mzero/pulsar-buddy/board/Pulsar Buddy SM grn.png

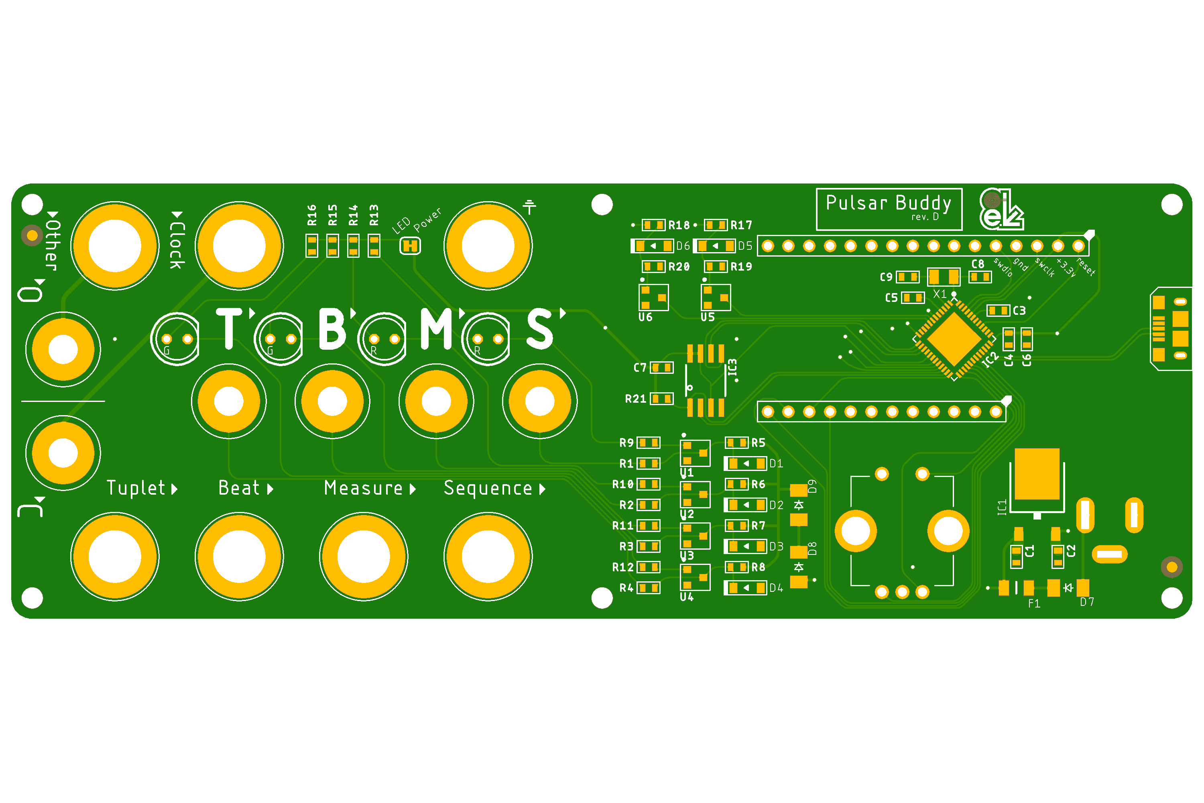
board/Pulsar Buddy SM grn.png
