mzero/pulsar-buddy/board/Pulsar Buddy SM.png

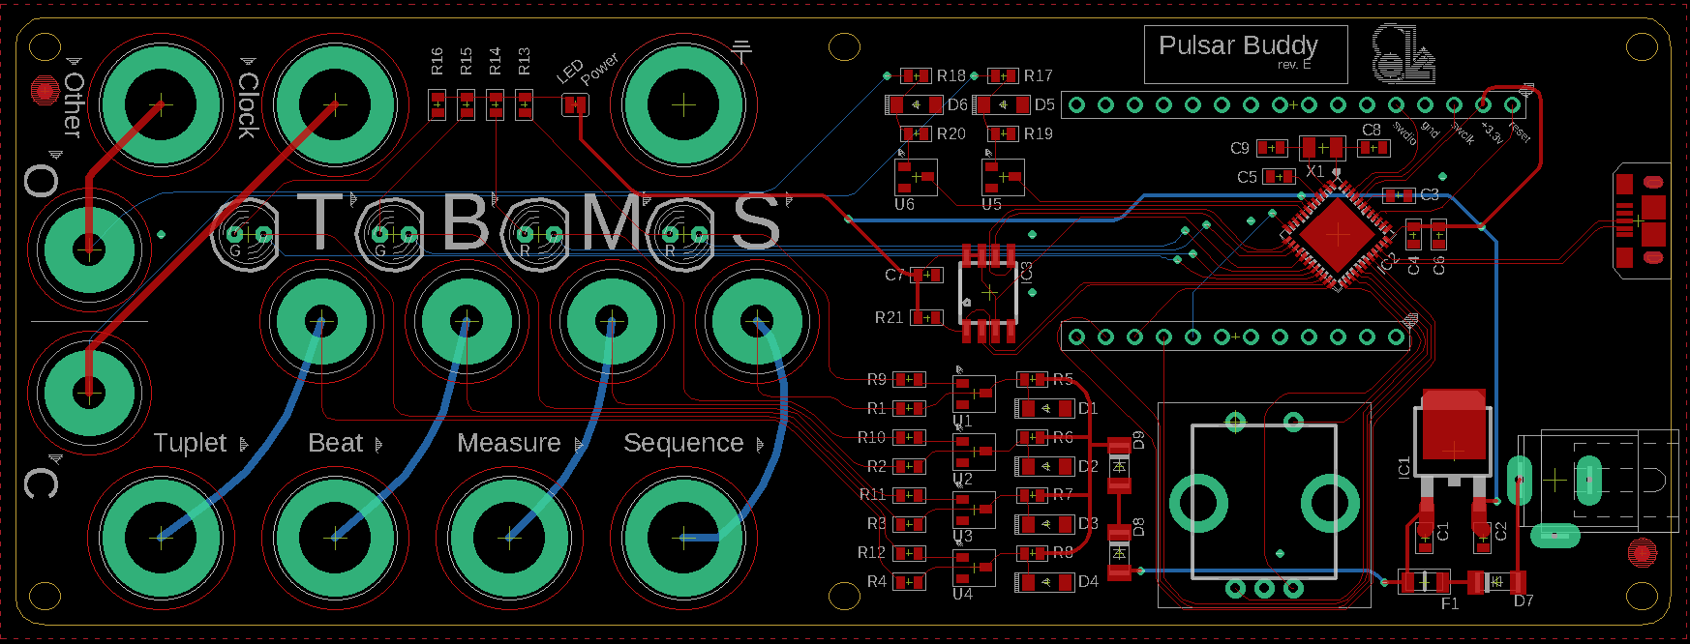
board/Pulsar Buddy SM.png
