mzero/pulsar-buddy/wiki-images/box1.jpg

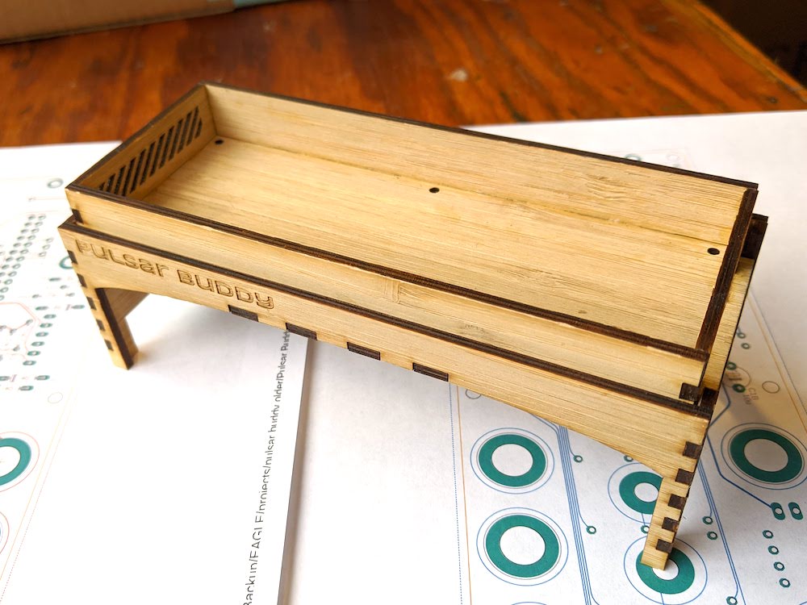
wiki-images/box1.jpg
