mzero/pulsar-buddy/wiki-images/box2.jpg

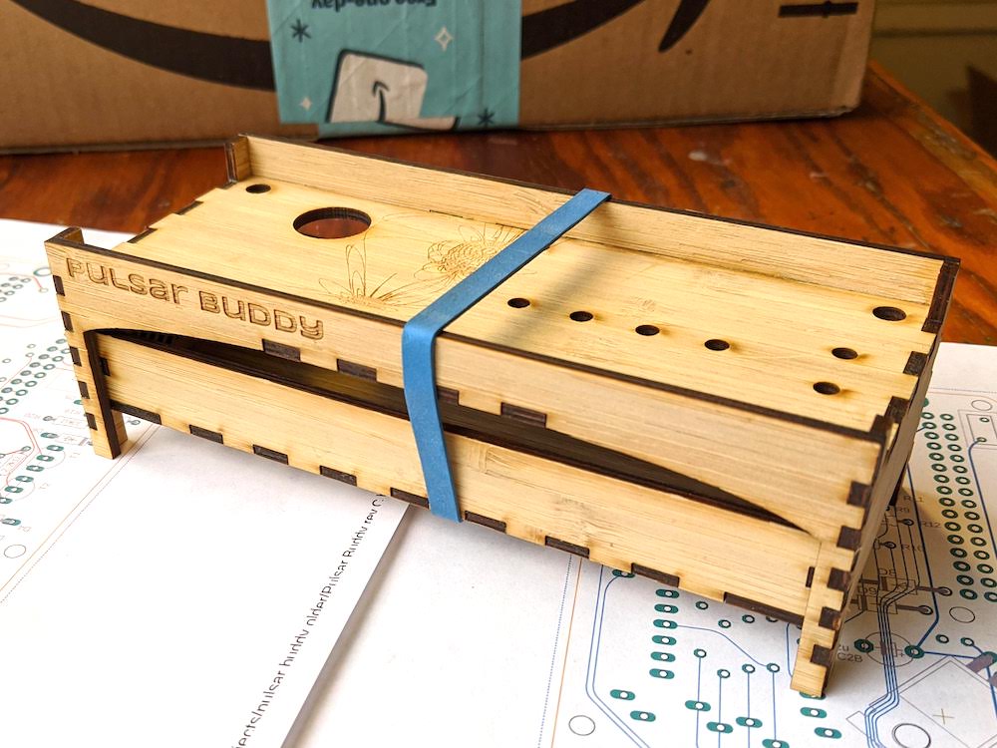
wiki-images/box2.jpg
