mzero/pulsar-buddy/wiki-images/box prototype.jpg

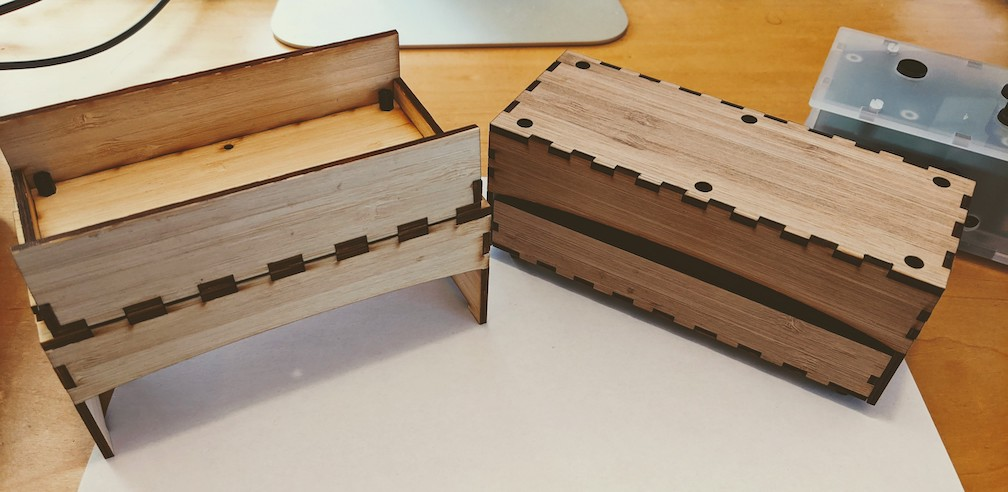
wiki-images/box prototype.jpg
