mzero/pulsar-buddy/wiki-images/pulsar buddy quick start.png

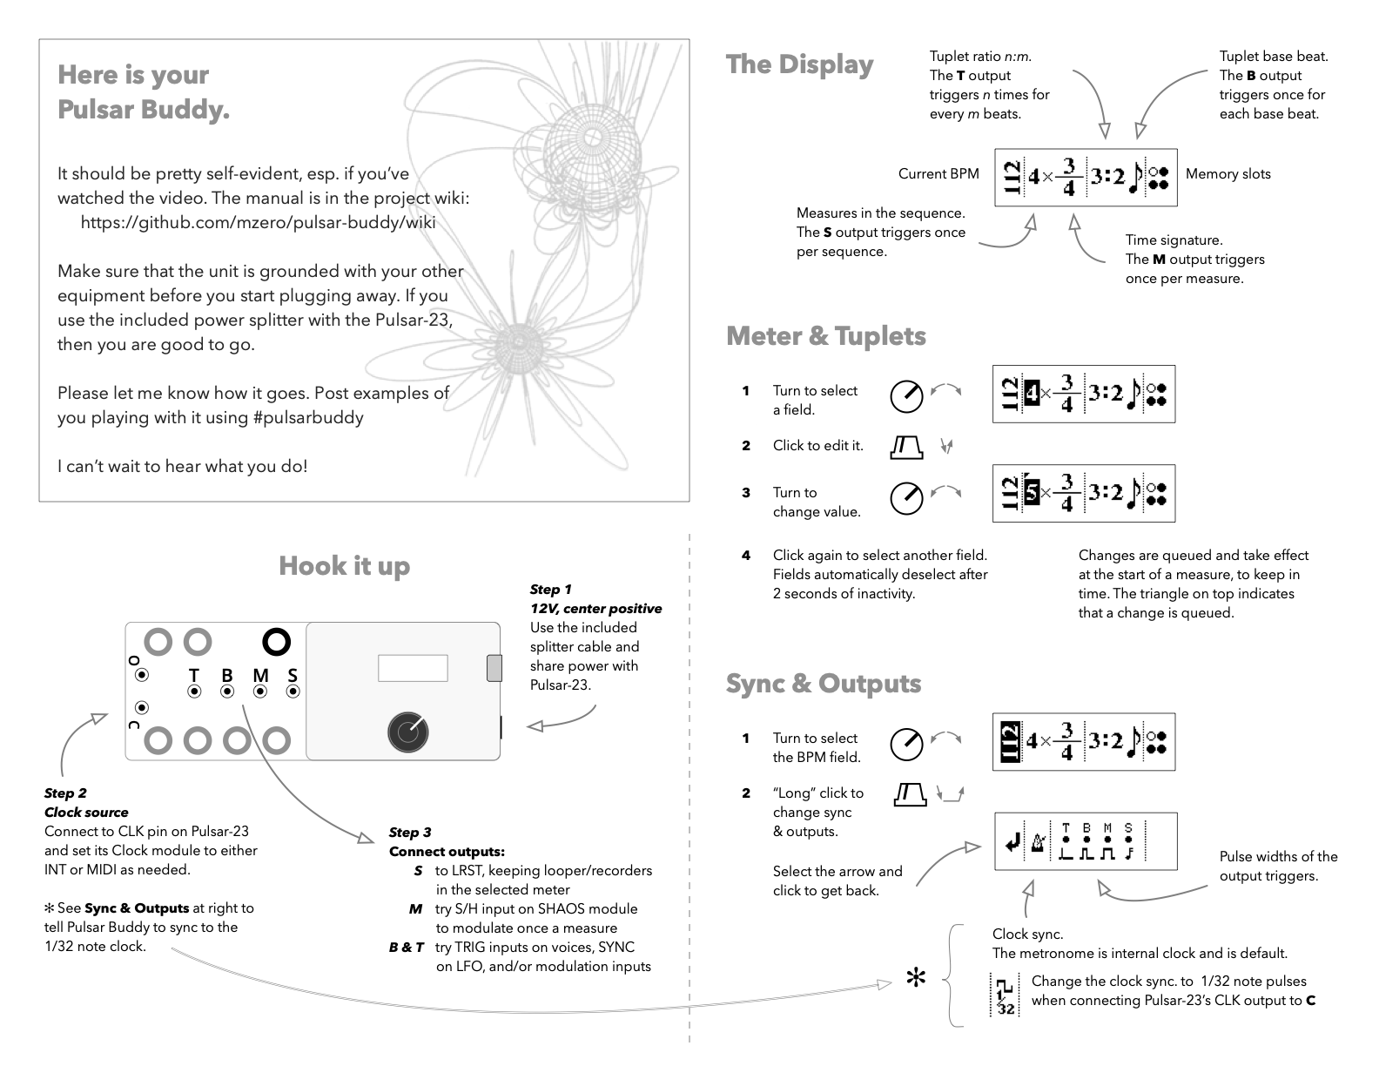
wiki-images/pulsar buddy quick start.png
