mzero/pulsar-buddy/wiki-images/rev B board.jpg

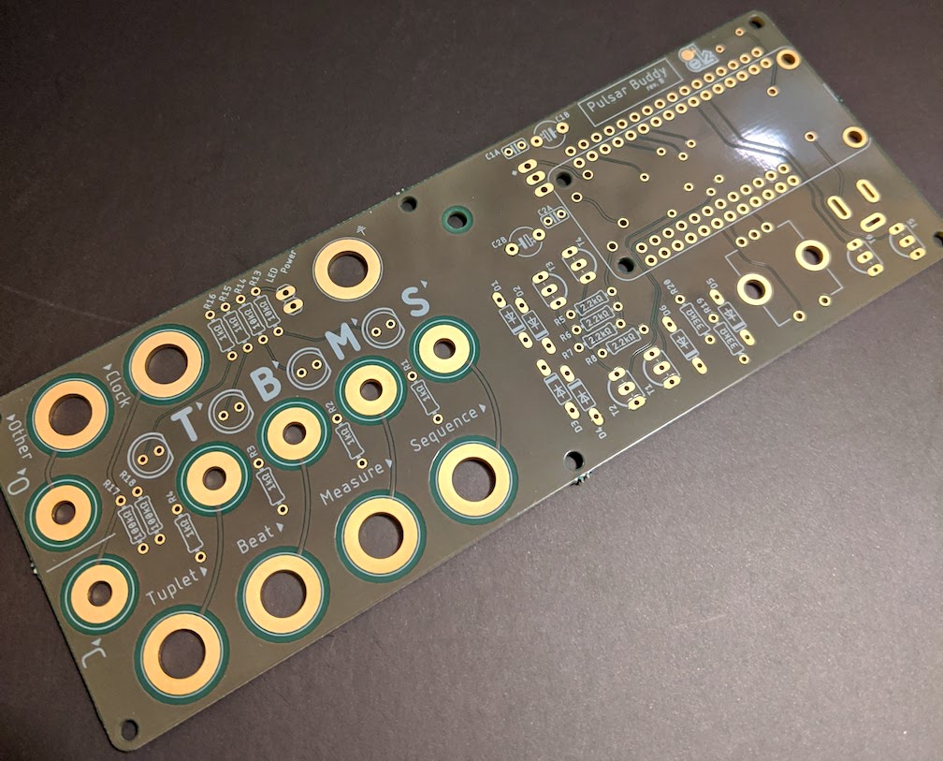
wiki-images/rev B board.jpg
