mzero/pulsar-buddy/wiki-images/unit.jpg

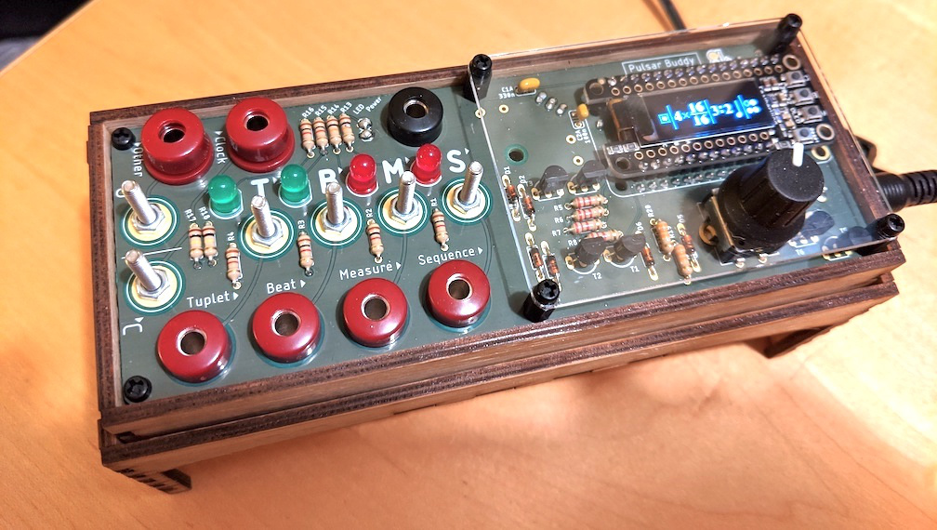
wiki-images/unit.jpg
