mzero/pulsar-buddy/wiki-images/assembly/E step 1 top.jpg

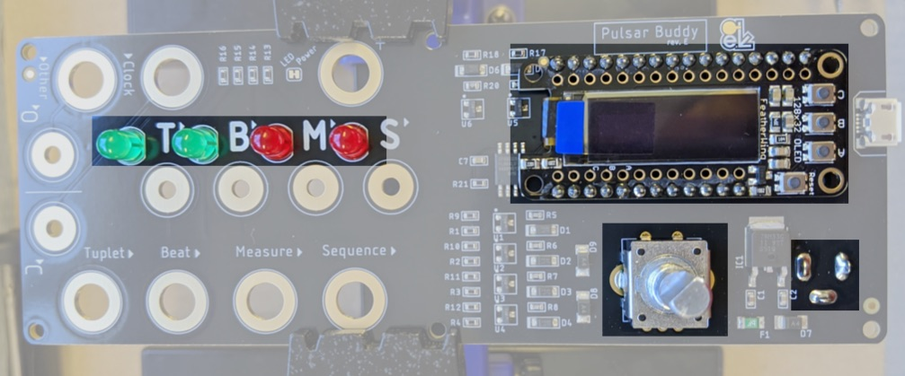
wiki-images/assembly/E step 1 top.jpg
