mzero/pulsar-buddy/wiki-images/assembly/E step 2 standoffs.jpg

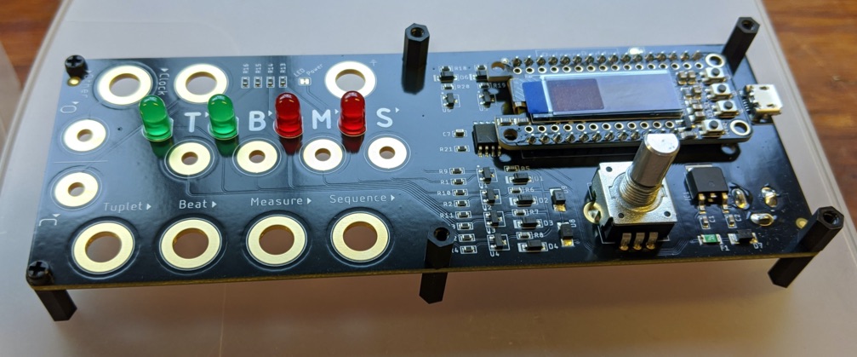
wiki-images/assembly/E step 2 standoffs.jpg
