mzero/pulsar-buddy/wiki-images/assembly/E step 3 connectors.jpg

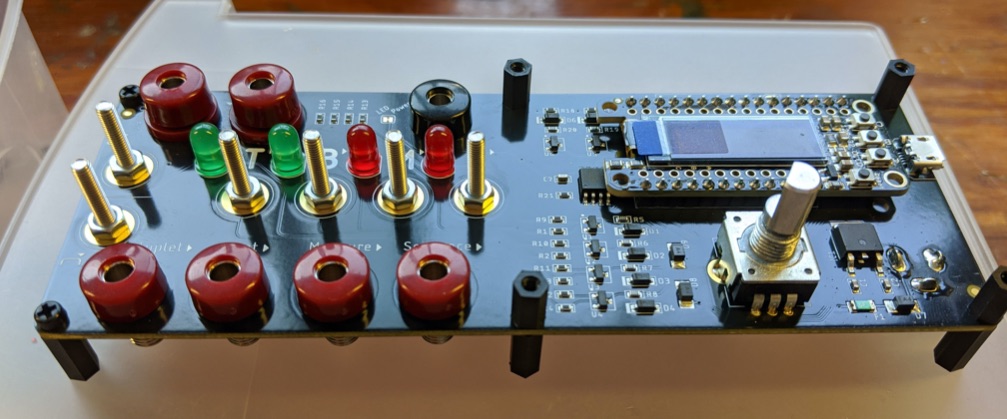
wiki-images/assembly/E step 3 connectors.jpg
