mzero/pulsar-buddy/wiki-images/assembly/step 3 top.jpg

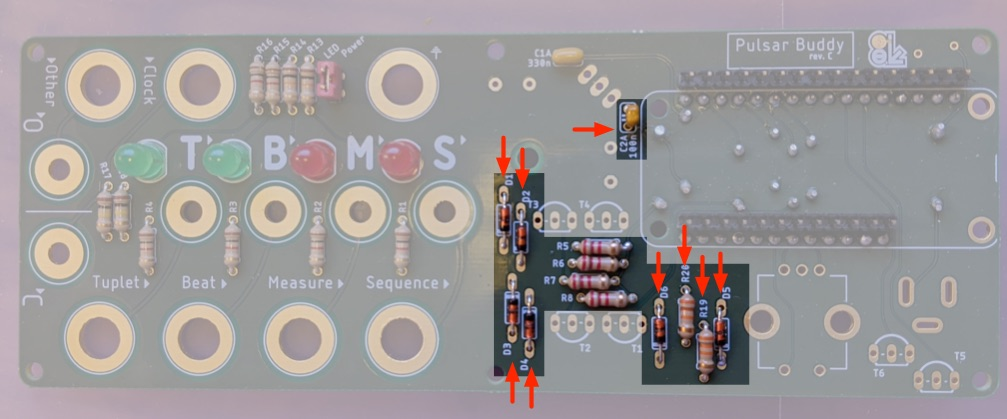
wiki-images/assembly/step 3 top.jpg
