mzero/pulsar-buddy/wiki-images/assembly/step 4 bottom.jpg

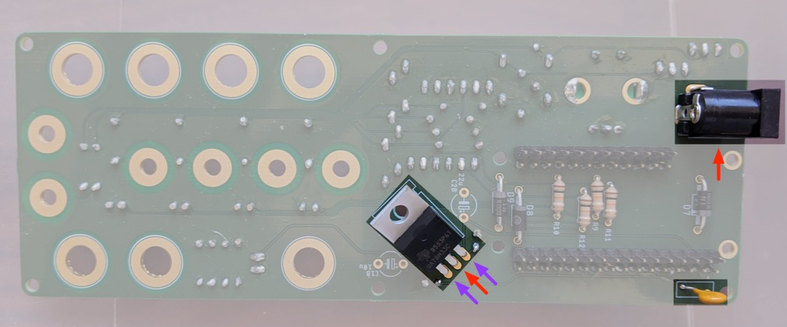
wiki-images/assembly/step 4 bottom.jpg
