mzero/pulsar-buddy/wiki-images/assembly/step 4 side.jpg

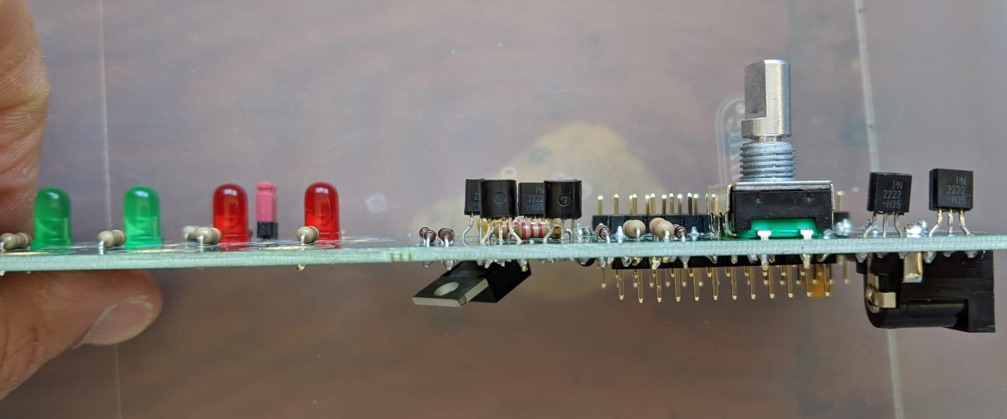
wiki-images/assembly/step 4 side.jpg
