mzero/pulsar-buddy/wiki-images/assembly/step 4 top.jpg

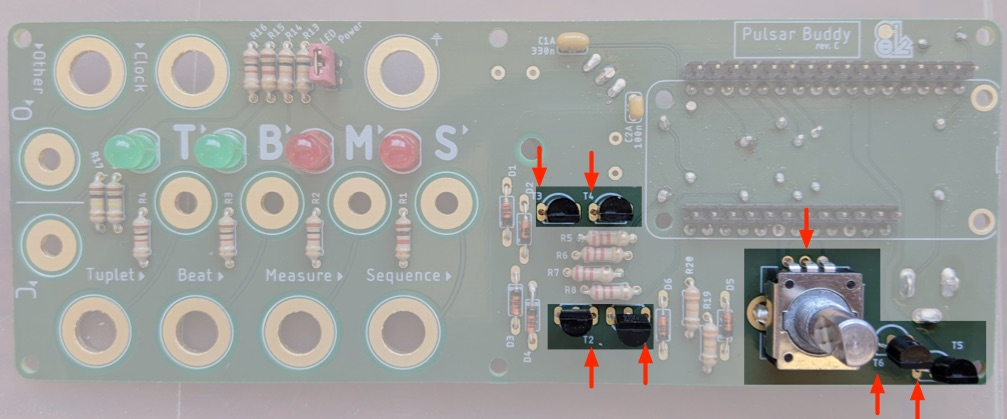
wiki-images/assembly/step 4 top.jpg
