mzero/pulsar-buddy/wiki-images/assembly/step 5 bottom.jpg

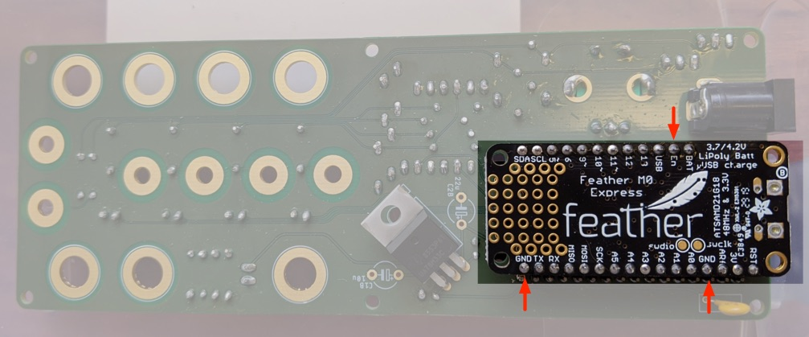
wiki-images/assembly/step 5 bottom.jpg
