mzero/pulsar-buddy/wiki-images/rev B build.jpg

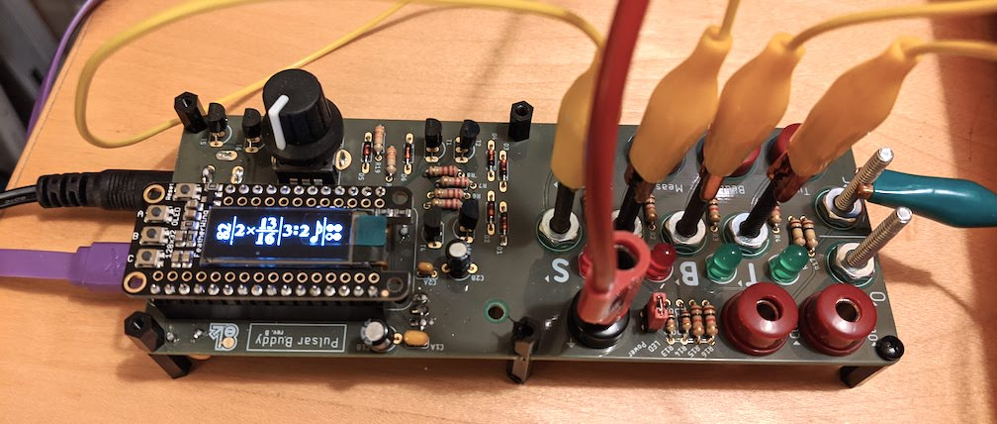
wiki-images/rev B build.jpg
