mzero/pulsar-buddy/pb/state.cpp

#include "state.h"

#include <Arduino.h>

#include "flash.h"


uint8_t syncPpqn(SyncMode sync) {
  if (sync == syncMidiUSB)
    return 24;
  if (syncExternalMin <= sync && sync <= syncExternalMax)
    return sync & syncExternalPPQNMask;
  return 0;
}

namespace {


  template <typename T, uint32_t currentVersion, size_t maxSize>
  class Container {

  public:
    bool begin(uint32_t startSector, uint32_t sectorCount);
    void save()
      { _log.save(_box); }

    T&       data()       { return _box._data; }
    const T& data() const { return _box._data; }

  private:
    static const uint32_t MAGIC = 1284161520 + maxSize;

    struct Box {
      uint32_t  _magic;
      uint32_t  _version;
      union {
        uint8_t _bytes[maxSize];
        T       _data;
      };

      Box() : _bytes() { }  // tell compiler which union member to construct
    };

    Box           _box;
    FlashLog<Box> _log;
  };

  template <typename T>
  void initialize(T& data)
      { data = T(); }

  template <typename T>
  bool upgrade(T&, uint32_t, const uint8_t*)
      { return false; }

  template <typename T, uint32_t currentVersion, size_t maxSize>
  bool Container<T, currentVersion, maxSize>::
    begin(uint32_t startSector, uint32_t sectorCount) {
      static_assert(sizeof(T) <= maxSize);

      _log.begin(startSector, sectorCount);

      _box._magic = 0;

      if (_log.load(_box)) {
        if (_box._magic == MAGIC) {
          if (_box._version == currentVersion) {
            return true;
          }

          T newData;
          if (upgrade(newData, _box._version, _box._bytes)) {
            _box._magic = MAGIC;
            _box._version = currentVersion;
            _box._data = newData;
            return true;
          }
        }
      }

      _box._magic = MAGIC;
      _box._version = currentVersion;
      initialize(_box._data);
      return false;
    }

}




namespace {
  State _userState;             // displayed in UI
  State _activeState;           // running on timers

  State _savedUserState;        // previous state, while displaying memories
  bool previewActive = false;


  typedef State State_v3;

  typedef State State_v2;
    // it is the same except for the added fields

  typedef Container<State_v3, 3, 40> StateContainer;
  StateContainer stateContainer;

  struct State_v1 {
    Settings    settings;
    uint8_t     memoryIndex;
    SyncMode    syncMode;
    uint16_t    userBpm;
    uint16_t    reserved;
  };

  bool upgrade2to3(State_v3& s, const State_v2& u) {
    s = u;
    s.otherSyncMode = otherSyncNone;
    return true;
  }

  bool upgrade1to3(State_v3& s, const State_v1& u) {
    s.settings = u.settings;
    s.memoryIndex = u.memoryIndex;
    s.syncMode = u.syncMode;
    s.userBpm = u.userBpm;
    // the only pulsewidth originally supported was pulseDuration16:
    s.pulseWidthS = pulseDuration16;
    s.pulseWidthM = pulseDuration16;
    s.pulseWidthB = pulseDuration16;
    s.pulseWidthT = pulseDuration16;
    s.outputModeS = outputSequence;
    s.outputModeM = outputMeasure;
    s.outputModeB = outputBeat;
    s.outputModeT = otuputTuplet;
    s.otherSyncMode = otherSyncNone;
    return true;
  }



  template<>
  bool upgrade(State_v3& s, uint32_t version, const uint8_t* bytes) {
    switch (version) {
      case 1:
        return upgrade1to3(s, *reinterpret_cast<const State_v1*>(bytes));
      case 2:
        return upgrade2to3(s, *reinterpret_cast<const State_v2*>(bytes));
    }
    return false;
  }


  State& _flashState = stateContainer.data();  // state pending write to flash
  unsigned long writeFlashAt = 0;

  bool sameState(const State& a, const State& b) {
    return memcmp(&a, &b, sizeof(State)) == 0;
  }
}

State& userState() { return _userState; }
const State& activeState() { return _activeState; }

bool pendingLoop() {
  if (previewActive) return false;
  return
       _userState.settings.numberMeasures  != _activeState.settings.numberMeasures
    || _userState.settings.beatsPerMeasure != _activeState.settings.beatsPerMeasure
    || _userState.settings.beatUnit        != _activeState.settings.beatUnit
    ;
}

bool pendingTuplet() {
  if (previewActive) return false;
  return
       _userState.settings.tupletCount != _activeState.settings.tupletCount
    || _userState.settings.tupletTime  != _activeState.settings.tupletTime
    || _userState.settings.tupletUnit  != _activeState.settings.tupletUnit
    ;
}

bool pendingMemory() {
  if (previewActive) return false;
  return
      _userState.memoryIndex != _activeState.memoryIndex;
}

bool pendingOutputSettings() {
  return
       _userState.pulseWidthS != _activeState.pulseWidthS
    || _userState.pulseWidthM != _activeState.pulseWidthM
    || _userState.pulseWidthB != _activeState.pulseWidthB
    || _userState.pulseWidthT != _activeState.pulseWidthT
    || _userState.outputModeS != _activeState.outputModeS
    || _userState.outputModeM != _activeState.outputModeM
    || _userState.outputModeB != _activeState.outputModeB
    || _userState.outputModeT != _activeState.outputModeT
    ;
}

bool pendingState() {
  if (previewActive) return false;
  return pendingLoop() || pendingTuplet() || pendingMemory()
    || pendingOutputSettings();
}

void commitState() {
  _activeState = _userState;

  _flashState = _userState;
  stateContainer.save();
  writeFlashAt = 0;
}

void persistState() {
  if (previewActive)
    return;

  if (!sameState(_flashState, _userState)) {
    _flashState = _userState;
    writeFlashAt = millis() + 2000;
    return;
  }

  if (writeFlashAt && writeFlashAt <= millis()) {
    stateContainer.save();
    writeFlashAt = 0;
  }
}



namespace {
  struct Storage_v1 {
    static const int numSlots = 4;

    Settings settings[numSlots];
  };

  template<>
  void initialize(Storage_v1& data) {
    static const Storage_v1 defaultStorage =
    { .settings =
      { { 4, 16, 16,    3, 2,  4 },
        { 4,  3,  4,    2, 3,  4 },
        { 2,  4,  4,    5, 4,  8 },
        { 2, 13, 16,    3, 2, 16 }
      }
    };

    data = defaultStorage;
  }

  Container<Storage_v1, 1, 112> storageContainer;



  typedef Storage_v1 Storage;

  inline Storage& storage() { return storageContainer.data(); }

  bool checkIndex(int i) {
    return 1 <= i && i <= Storage::numSlots;
  }

}


void loadFromMemory(int index) {
  if (!checkIndex(index))
    return;

  _userState.memoryIndex = index;
  _userState.settings = storage().settings[index-1];
}

void storeToMemory(int index) {
  if (!checkIndex(index))
    return;

  _userState.memoryIndex = index;
  storage().settings[index-1] = _userState.settings;

  storageContainer.save();
}

void loadNextMemory() {
  int i = _activeState.memoryIndex;
  i = i - 1; // make zero based
  i = (i + 1) % Storage::numSlots;
  i = i + 1; // make one based
  loadFromMemory(i);
}

void showMemoryPreview(int index) {
  if (!previewActive) {
    _savedUserState = _userState;
    previewActive = true;
  }
  loadFromMemory(index);
}

void endMemoryPreview() {
  if (previewActive) {
    _userState = _savedUserState;
    previewActive = false;
  }
}


/* FLASH USAGE

  The Feather M0 Express has 2MB of Flash, or 512 pages.
  The Pulsar Buddy rev. D & E boards have 8MB of Flash, or 2048 pages.

  Storage here is sized to fit in 2MB, leaving some space for future options.

  Sectors         Versions      Format & Purpose
    0 ~   7       v100 ~ v105   LogContainer<State_v1>
    8 ~  15       v100 ~ v105   Container<Storage>
   16 ~  23       all           LogContainer<Configuration> (see config.cpp)
   32 ~ 191       v106 ~ on     Container<State>
  129 ~ 351       v106 ~ on     Container<Storage>

*/

void initializeState() {
  bool stateLoaded = stateContainer.begin(32, 160);
  if (!stateLoaded) {
    FlashLog<State_v1> oldStateLog;
    if (oldStateLog.begin(0, 8)) {
      State_v1 oldState;
      if (oldStateLog.load(oldState)) {
        if (upgrade1to3(_flashState, oldState)) {
          stateContainer.save();
          stateLoaded = true;
        }
      }
    }
  }

  bool storageLoaded = storageContainer.begin(192, 160);
  if (!storageLoaded) {
    Container<Storage_v1, 1, 112> oldStorageContainer;
    if (oldStorageContainer.begin(8, 8)) {
      storageContainer.data() = oldStorageContainer.data();
      storageContainer.save();
      storageLoaded = true;
    }
  }

  if (stateLoaded) {
    _userState = _activeState = _flashState;
  } else {
    loadFromMemory(1);
    commitState();
  }
}
