mzero/pulsar-buddy/pb/controls.h

#ifndef _INCLUDE_CONTROLS_H_
#define _INCLUDE_CONTROLS_H_

#include "ui_input.h"
extern IdleTimeout selectionTimeout;
extern IdleTimeout dimTimeout;

extern Encoder encoder;
extern Button encoderButton;

extern Button oledButtonA;
extern Button oledButtonB;
extern Button oledButtonC;

#endif // _INCLUDE_CONTROLS_H_
