mzero/pulsar-buddy/pb/flash.cpp

#include "flash.h"

#include <initializer_list>

#include "Adafruit_SPIFlashBase.h"

#include "config.h"
#include "critical.h"


namespace {

  #if defined(__SAMD51__) || defined(NRF52840_XXAA)
    Adafruit_FlashTransport_QSPI flashTransport(PIN_QSPI_SCK, PIN_QSPI_CS, PIN_QSPI_IO0, PIN_QSPI_IO1, PIN_QSPI_IO2, PIN_QSPI_IO3);
  #else
    #if (SPI_INTERFACES_COUNT == 1 || defined(ADAFRUIT_CIRCUITPLAYGROUND_M0))
      Adafruit_FlashTransport_SPI flashTransport(SS, &SPI);
    #else
      Adafruit_FlashTransport_SPI flashTransport(SS1, &SPI1);
    #endif
  #endif
}

  Adafruit_SPIFlashBase flash(&flashTransport);

namespace {
  bool flashBegun = false;

  const std::initializer_list<SPIFlash_Device_t> additional_devices = {
    // Settings for the Cypress (was Spansion) S25FL064L 8MiB SPI flash.
    // Datasheet: http://www.cypress.com/file/316661/download
    {
      .total_size = (1 << 23), /* 8 MiB */
          .start_up_time_us = 300, .manufacturer_id = 0x01, .memory_type = 0x60,
      .capacity = 0x17,
      .max_clock_speed_mhz = 4,
          // Speeed must be limited due to bad routing on board (for caop. C7),
          // 12MHz works in tests 100% reliably, but picking 4 just to be safe.
      .quad_enable_bit_mask = 0x02, .has_sector_protection = false,
      .supports_fast_read = true, .supports_qspi = true,
      .supports_qspi_writes = true, .write_status_register_split = false,
      .single_status_byte = false,
    }
  };

  /* Header

    The header of each sector starts with a 4-byte magic number, which is used
    as a guard against reading random data as valid. And a serial number
    of the sector, so that after wrapping one can find which is the newest
    sector (since all will be valid).

  */
  struct Header {
    uint32_t magic;
    uint32_t serial;
  };

  uint32_t computeMagicValue(uint32_t a, uint32_t b, uint32_t c) {
    return (
      1176328692                // tracking number of my first Adafruit order
      ^ (a + 123) * 0x08040201  // spread out every 9 bits
      ^ (b + 456) * 0x20100401  // spread out every 10 bits
      ^ (c + 789) * 0x10204081  // spread out every 7 bits
      ) & ~0x1;                 // must have at least one zero
  }

  const uint32_t notFoundSerial = 0;    // must be smallest value
  const uint32_t firstSerial = 1;


  /* Layout
    Each sector has this layout:

      [Header|bitmap|entry0|entry1|...|entry n]
  */


  struct Layout {
    const uint32_t dataLength;
    const uint32_t entriesPerSector;
    const uint32_t bitmapLength;

    Layout(uint32_t dataLength);

    static const uint32_t maxDataLength
      = SFLASH_SECTOR_SIZE - sizeof(Header) - 1;

    static inline uint32_t headerAddress(uint32_t sector)
      { return sector * SFLASH_SECTOR_SIZE; }

    static inline uint32_t bitmapAddress(uint32_t sector)
      { return headerAddress(sector) + sizeof(Header); }

    inline uint32_t dataAddress(uint32_t sector, uint32_t index) const {
      { return bitmapAddress(sector) + bitmapLength + index * dataLength; }
    }
  };

  Layout::Layout(uint32_t dataLength)
    : dataLength(dataLength),
      entriesPerSector(
        (8 * (SFLASH_SECTOR_SIZE - sizeof(Header))
        / (8 * dataLength + 1))),
      bitmapLength((entriesPerSector + 7) / 8)
    { }

}


bool FlashMemoryLog::begin(uint32_t startSector, uint32_t sectorCount)
{
  regionStartSector = startSector;
  regionEndSector = startSector + sectorCount;
  regionMagicValue = computeMagicValue(dataLength, startSector, sectorCount);
  currentSerial = notFoundSerial;
  currentSector = 0;
  currentIndex = 0;

  if (!flashBegun) {
    if (!flash.begin(additional_devices.begin(), additional_devices.size())) {
      critical.println("flash begin failure");
      return false;
    }
    if (configuration.debug.flash) {
      Serial.printf("flash length in sectors: %d\n",
        flash.size() / SFLASH_SECTOR_SIZE);
    }
    flashBegun = true;
  }


  if (dataLength > Layout::maxDataLength) {
    critical.println("data length too big");
    return false;
  }

  if ((regionEndSector - regionStartSector) < 2) {
    critical.println("must have at least 2 sectors in region");
    return false;
  }

  uint32_t numberOfSectors = flash.size() / SFLASH_SECTOR_SIZE;

  if (regionStartSector >= numberOfSectors) {
    critical.println("start sector beyond flash capacity");
    return false;
  }

  if (regionEndSector > numberOfSectors) {
    critical.println("region extends past end of flash");
    return false;
  }

  auto layout = Layout(dataLength);

  currentSerial = notFoundSerial;
  currentSector = 0;

  for (uint32_t sector = regionStartSector;
       sector < regionEndSector;
       ++sector)
  {
    Header header;
    if (flash.readBuffer(layout.headerAddress(sector),
          reinterpret_cast<uint8_t*>(&header),
          sizeof(header))
        != sizeof(header))
    {
      critical.printf("flash read failure at sector %d\n", sector);
      return false;
    }

    if (header.magic != regionMagicValue)
      // can't be our data from here on after
      break;
    if (header.serial < currentSerial)
      // older sector, as will be all that follow
      break;

    currentSerial = header.serial;
    currentSector = sector;
  }

  if (currentSerial != notFoundSerial) {
    currentIndex = 0;

    uint8_t bitMap[layout.bitmapLength];
    if (flash.readBuffer(layout.bitmapAddress(currentSector),
          bitMap, layout.bitmapLength)
        != layout.bitmapLength)
    {
      critical.printf("flash read failure of bitmap at sector %d\n",
        currentSector);
      return false;
    }

    for (uint32_t mapIndex = 0; mapIndex < layout.bitmapLength; mapIndex++)
    {
      switch (bitMap[mapIndex]) {
        case 0x00:  currentIndex = mapIndex * 8 + 7; break;
        case 0x80:  currentIndex = mapIndex * 8 + 6; goto found;
        case 0xc0:  currentIndex = mapIndex * 8 + 5; goto found;
        case 0xe0:  currentIndex = mapIndex * 8 + 4; goto found;
        case 0xf0:  currentIndex = mapIndex * 8 + 3; goto found;
        case 0xf8:  currentIndex = mapIndex * 8 + 2; goto found;
        case 0xfc:  currentIndex = mapIndex * 8 + 1; goto found;
        case 0xfe:  currentIndex = mapIndex * 8    ; goto found;
        case 0xff:  goto found;
        default:
          // something is very amiss
          // reset region
          critical.printf("bitmap was ill formed in sector %d\n",
            currentSector);
          currentSector = notFoundSerial;
          goto found;
      }
    }
found:    // sometimes, a goto is just the thing!
    ;
  }

  if (configuration.debug.flash) {
    Serial.println("FlashMemoryLog begin:");
    Serial.printf( "   data length        = %4d\n", layout.dataLength);
    Serial.printf( "   entries per sector = %4d\n", layout.entriesPerSector);
    Serial.printf( "   bitmap length      = %4d\n", layout.bitmapLength);
    Serial.printf( "   current serial     = %4d\n", currentSerial);
    Serial.printf( "   current sector     = %4d\n", currentSector);
    Serial.printf( "   current index      = %4d\n", currentIndex);
  }
  return true;
}


bool FlashMemoryLog::readCurrent(uint8_t* buf)
{
  if (currentSerial == notFoundSerial)
    return false;

  auto layout = Layout(dataLength);

  return
    flash.readBuffer(layout.dataAddress(currentSector, currentIndex),
      buf, dataLength)
    == dataLength;
}

bool FlashMemoryLog::writeNext(const uint8_t* buf)
{
  auto layout = Layout(dataLength);

  uint32_t nextSerial = currentSerial;
  uint32_t nextSector;
  uint32_t nextIndex;

  if (nextSerial == notFoundSerial) {
    nextSerial = firstSerial;
    nextSector = regionStartSector;
    nextIndex = 0;
  } else {
    nextSector = currentSector;
    nextIndex = currentIndex + 1;

    if (nextIndex >= layout.entriesPerSector) {
      nextSerial = nextSerial + 1;
      nextSector = nextSector + 1;
      nextIndex = 0;

      if (nextSector >= regionEndSector) {
        nextSector = regionStartSector;   // wrap
      }
    }
  }

  if (nextIndex == 0) {
    if (!flash.eraseSector(nextSector)) {
      critical.printf("sector %d failed to erase\n", nextSector);
      return false;
    }

    Header header;
    header.magic = regionMagicValue;
    header.serial = nextSerial;

    if (flash.writeBuffer(layout.headerAddress(nextSector),
          reinterpret_cast<uint8_t*>(&header), sizeof(Header))
      != sizeof(Header))
    {
      critical.printf("header write failed, sector %d\n", nextSector);
      return false;
    }
  }

  if (flash.writeBuffer(layout.dataAddress(nextSector, nextIndex),
        buf, dataLength)
      != dataLength)
  {
    critical.printf("data write failed, sector %d index %d\n",
      nextSector, nextIndex);
    return false;
  }

  uint8_t bitmapByte = 0xff << ((nextIndex & 0x07) + 1);

  if (flash.writeBuffer(layout.bitmapAddress(nextSector) + nextIndex / 8,
      &bitmapByte, 1)
      != 1)
  {
    critical.printf("bitmap write failed, sector %d index %d\n",
      nextSector, nextIndex);
    return false;
  }

  currentSerial = nextSerial;
  currentSector = nextSector;
  currentIndex = nextIndex;

  if (configuration.debug.flash) {
    Serial.println("FlashMemoryLog wrote:");
    Serial.printf("   current serial     = %4d\n", currentSerial);
    Serial.printf("   current sector     = %4d\n", currentSector);
    Serial.printf("   current index      = %4d\n", currentIndex);
  }

  return true;
}
