mzero/pulsar-buddy/pb/timer_hw.h

#ifndef _INCLUDE_TIMER_HW_H_
#define _INCLUDE_TIMER_HW_H_

#include "timing.h"

void initializeTimers();

extern void isrMeasure();
extern void isrMidiClock();
extern void isrClockCapture(q_t);
extern void isrWatchdog();
extern void isrOtherSync(bool);


typedef uint16_t divisor_t;     // the quantum timer has a 16 bit counter
float divisorToBpm(divisor_t);
divisor_t divisorFromBpm(float);

void setQuantumDivisor(divisor_t);
void startQuantumEvents();
void stopQuantumEvents();

class PauseQuantum {
public:
  PauseQuantum();
  ~PauseQuantum();
private:
  bool wasRunning;
};


void readCounts(Offsets&);
q_t  readSequenceCount();
void writeCounts(const Offsets&);
void writePeriods(const Timing&, divisor_t);
void updateWidths(divisor_t, const Timing&);

void disableTriggers(bool off, bool force = false);

void resetWatchdog(q_t);
q_t readWatchdog();

enum ExtClockSource {
  extClockHardware,
  extClockSoftware,
};

void useExtClockSource(ExtClockSource);
void softwareExtClock();

void dumpTimers();

#endif // _INCLUDE_TIMER_HW_H_
