mzero/pulsar-buddy/pb/ui_sync.cpp

#include "ui_sync.h"

#include "display.h"
#include "layout.h"


namespace SyncImages {
  const unsigned char paused[] = { // 15 x 32
    0x00, 0x00, 0x00, 0x00, 0x00, 0x00, 0x00, 0x00, 0x00, 0x00, 0x00, 0x00, 0x00, 0x00, 0x00, 0x00,
    0x00, 0x00, 0x00, 0x00, 0x2a, 0xa8, 0x00, 0x00, 0x20, 0x08, 0x06, 0xc0, 0x26, 0xc8, 0x06, 0xc0,
    0x26, 0xc8, 0x06, 0xc0, 0x20, 0x08, 0x00, 0x00, 0x2a, 0xa8, 0x00, 0x00, 0x00, 0x00, 0x00, 0x00,
    0x00, 0x00, 0x00, 0x00, 0x00, 0x00, 0x00, 0x00, 0x00, 0x00, 0x00, 0x00, 0x00, 0x00, 0x00, 0x00,
  };
  const unsigned char din24[] = { // 15 x 32
    0x00, 0x00, 0x00, 0x00, 0x00, 0x00, 0x00, 0x00, 0x00, 0x00, 0x03, 0x80, 0x0f, 0xe0, 0x1f, 0xf0,
    0x1f, 0xf0, 0x3f, 0xf8, 0x37, 0xd8, 0x3f, 0xf8, 0x1b, 0xb0, 0x1e, 0xf0, 0x0f, 0xe0, 0x03, 0x80,
    0x00, 0x00, 0x00, 0x00, 0x1c, 0x18, 0x3e, 0x38, 0x46, 0x38, 0x06, 0x58, 0x0c, 0x98, 0x18, 0xfc,
    0x30, 0xfc, 0x7e, 0x18, 0x7e, 0x18, 0x00, 0x00, 0x00, 0x00, 0x00, 0x00, 0x00, 0x00, 0x00, 0x00,
  };
  const unsigned char din48[] = { // 15 x 32
    0x00, 0x00, 0x00, 0x00, 0x00, 0x00, 0x00, 0x00, 0x00, 0x00, 0x03, 0x80, 0x0f, 0xe0, 0x1f, 0xf0,
    0x1f, 0xf0, 0x3f, 0xf8, 0x37, 0xd8, 0x3f, 0xf8, 0x1b, 0xb0, 0x1e, 0xf0, 0x0f, 0xe0, 0x03, 0x80,
    0x00, 0x00, 0x00, 0x00, 0x0c, 0x70, 0x1c, 0xd8, 0x1c, 0xd8, 0x2c, 0x70, 0x4c, 0xb8, 0x7e, 0xd8,
    0x7e, 0xd8, 0x0c, 0xd8, 0x0c, 0x70, 0x00, 0x00, 0x00, 0x00, 0x00, 0x00, 0x00, 0x00, 0x00, 0x00,
  };
  const unsigned char dinmidi[] = { // 15 x 32
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
    0x00, 0x00, 0x00, 0x00, 0x00, 0x00, 0x00, 0x00, 0x0c, 0x60, 0x12, 0xf0, 0x12, 0xf0, 0x0c, 0x60,
    0x00, 0x00, 0x0c, 0x60, 0x1e, 0xf0, 0x1e, 0xf0, 0x0c, 0x60, 0x00, 0x00, 0x00, 0x00, 0x00, 0x00,
  };
}



/**
 **  BPM Field
 **/

bool BpmField::isOutOfDate() {
  auto status = ClockStatus::current();

  return
    (clockAsDrawn != status)
    || Field::isOutOfDate();
}

void BpmField::enter(bool alternate) {
  if (alternate) {
    showSetup();
    return;
  }
}


void BpmField::update(Encoder::Update update) {
  auto status = ClockStatus::current();

  setBpm(status.bpm + update.accel(5));
}

void BpmField::redraw() {

  display.setTextColor(foreColor());

  auto status = ClockStatus::current();

  if (status.advancing()) {
    switch (status.state) {
      case clockFreeRunning:
      case clockSyncRunning: {
        // rotated coordinates of the field
        const int16_t xr = display.height() - (y + h);
        const int16_t yr = x;
        const int16_t wr = h;
        const int16_t hr = w;

        setRotationSideways();
        centerNumber(status.bpm, xr, yr, wr, hr);
        setRotationNormal();

        break;
      }

      case clockPerplexed: {
        auto image = SyncImages::clkbad;
        switch (state.syncMode) {
          case syncExternal24ppqn:
          case syncExternal48ppqn:
            image = SyncImages::dinbad;
            break;
          default:
            break;
        }
        display.drawBitmap(x, y, image, 15, 32, foreColor());
        break;
      }

      case clockPaused:
        // can't happen if advancing()!
        break;
    }
  } else {
    // user sees the paused symbol if the clock isn't advancing
    display.drawBitmap(x, y, SyncImages::paused, 15, 32, foreColor());

    // if we still have sync of some sort, display it tiny at the bottom
    switch (status.state) {
      case clockFreeRunning:
      case clockSyncRunning:
        tinyText();
        centerNumber(status.bpm, x, y + h - 8, w, 8);
        resetText();
        break;

      case clockPerplexed:
        tinyText();
        centerText("???", x, y + h - 8, w, 8);
        resetText();
        break;

      default:
        break;
    }
  }

  clockAsDrawn = status;
}


/**
 **  Sync Field
 **/

bool SyncField::isOutOfDate() {
  return
    (syncAsDrawn != pendingSync)
    || Field::isOutOfDate();
}

void SyncField::enter(bool alternate) {
  pendingSync = state.syncMode;
  pending = true;
}

void SyncField::exit() {
  state.syncMode = pendingSync;
  pending = false;
  setSync(state.syncMode);
}

namespace {
  struct SyncInfo {
    SyncMode              mode;
    const unsigned char * image;
  };

  SyncInfo syncOptions[] = {
    { syncInternal,       SyncImages::internal },
    { syncExternal1ppqn,  SyncImages::clk4 },
    { syncExternal2ppqn,  SyncImages::clk8 },
    { syncExternal4ppqn,  SyncImages::clk16 },
    { syncExternal8ppqn,  SyncImages::clk32 },
    { syncExternal24ppqn, SyncImages::din24 },
    { syncExternal48ppqn, SyncImages::din48 },
    { syncMidiUSB,        SyncImages::usbmidi },
  };

  const int numSyncOptions = sizeof(syncOptions) / sizeof(syncOptions[0]);

  int findSyncModeIndex(SyncMode sync) {
    for (int i = 0; i < numSyncOptions; ++i) {
      if (sync == syncOptions[i].mode)
        return i;
    }
    return -1;
  }
}

void SyncField::update(Encoder::Update update) {
  int i = findSyncModeIndex(pendingSync);
  int j = constrain(i + update.dir(), 0, numSyncOptions - 1);
  pendingSync = syncOptions[j].mode;
}

void SyncField::redraw() {
  auto s = pending ? pendingSync : state.syncMode;

  display.setTextColor(foreColor());

  int i = findSyncModeIndex(s);
  if (i >= 0)
    display.drawBitmap(x, y, syncOptions[i].image, 15, 32, foreColor());
  else
    centerText("?", x, y, w, h);
  syncAsDrawn = s;
}


/**
 **  OtherSync Field
 **/

bool OtherSyncField::isOutOfDate() {
  return
    (syncAsDrawn != pendingSync)
    || Field::isOutOfDate();
}

void OtherSyncField::enter(bool alternate) {
  pendingSync = state.otherSyncMode;
  pending = true;
}

void OtherSyncField::exit() {
  state.otherSyncMode = pendingSync;
  pending = false;
  setOtherSync(state.otherSyncMode);
}

namespace {
  struct OtherSyncInfo {
    OtherSyncMode         mode;
    const unsigned char * image;
  };

  OtherSyncInfo otherSyncOptions[] = {
    { otherSyncNone,            OtherSyncImages::none },

    { otherSyncRunStop,         OtherSyncImages::dinstart },
    { otherSyncRunPause,        OtherSyncImages::dinrun },
    { otherSyncRunStopToggle,   OtherSyncImages::trigstart },
    { otherSyncRunPauseToggle,  OtherSyncImages::trigrun },

    { otherSyncAlignBeat,       OtherSyncImages::align1 },
    { otherSyncAlign2Beat,      OtherSyncImages::align2 },
    { otherSyncAlign4Beat,      OtherSyncImages::align4 },
    { otherSyncAlignMeasure,    OtherSyncImages::alignM2 },
    { otherSyncAlignSequence,   OtherSyncImages::alignS2 },

    { otherSyncNextSettings,    OtherSyncImages::next },
  };

  const int numotherSyncOptions = sizeof(otherSyncOptions) / sizeof(otherSyncOptions[0]);

  int findOtherSyncModeIndex(OtherSyncMode sync) {
    for (int i = 0; i < numotherSyncOptions; ++i) {
      if (sync == otherSyncOptions[i].mode)
        return i;
    }
    return -1;
  }
}

void OtherSyncField::update(Encoder::Update update) {
  int i = findOtherSyncModeIndex(pendingSync);
  int j = constrain(i + update.dir(), 0, numotherSyncOptions - 1);
  pendingSync = otherSyncOptions[j].mode;
}

void OtherSyncField::redraw() {
  auto s = pending ? pendingSync : state.otherSyncMode;

  int i = findOtherSyncModeIndex(s);
  if (i >= 0)
    display.drawBitmap(x, y, otherSyncOptions[i].image, 15, 32, foreColor());
  else
    centerText("?", x, y, w, h);
  syncAsDrawn = s;
}

namespace ReturnImage {
  const unsigned char returnArrow[] = { // 15 x 22
    0x00, 0x00, 0x00, 0x00, 0x00, 0x00, 0x00, 0x00, 0x00, 0x38, 0x00, 0x38, 0x00, 0x38, 0x00, 0x38,
    0x00, 0x38, 0x00, 0x38, 0x02, 0x38, 0x06, 0x38, 0x0e, 0x78, 0x1f, 0xf0, 0x3f, 0xf0, 0x1f, 0xc0,
    0x0e, 0x00, 0x06, 0x00, 0x02, 0x00, 0x00, 0x00, 0x00, 0x00, 0x00, 0x00,
  };
}

void ReturnField::enter(bool alternate) {
  showMain();
}

void ReturnField::redraw() {
  display.drawBitmap(x, y, ReturnImage::returnArrow, 15, 22, foreColor());
}
