mzero/pulsar-buddy/pb/ui_layout.h

#ifndef _INCLUDE_UI_LAYOUT_H_
#define _INCLUDE_UI_LAYOUT_H_

#include <initializer_list>

#include "ui_field.h"


class Layout : public Field {
public:
  Layout(const std::initializer_list<Field*>& f, int initialSelectedIndex = 0)
    : Field(0, 0, 128, 32), // FIXME: hack!! compute from field list
      fields(f), selectedIndex(initialSelectedIndex), focus(focusNone)
    { }

  bool render(bool refresh);
  void select(bool s);

  void enter(bool alternate);
  void exit();

  bool click(Button::State s);
  void update(Encoder::Update);

protected:
  const std::initializer_list<Field*>& fields;
  int selectedIndex;

  Field* selectedField() const;

  enum Focus { focusNone, focusNavigate, focusField };
  Focus focus;

  void redraw();
};

class Frame : public Field {
public:
  Frame(Field* c = nullptr)
    : Field(0, 0, 128, 32), // FIXME: hack!! where can we get this?
      content(nullptr), drawnContent(nullptr)
    { show(c); }
  Frame(Field& c) : Frame(&c) { }

  void show(Field* c);
  void show(Field& c) { show(&c); }
  void clear()        { show(nullptr); }

  bool render(bool refresh);
  void select(bool s);

  void enter(bool alternate);
  void exit();

  bool click(Button::State s);
  void update(Encoder::Update);

protected:
  Field* content;
  Field* drawnContent;

  bool isOutOfDate();
  void redraw();
};


#endif // _INCLUDE_UI_LAYOUT_H_
