mzero/pulsar-buddy/pb/ui_input.h

#ifndef _INCLUDE_UI_INPUT_H_
#define _INCLUDE_UI_INPUT_H_

#include <stdint.h>


class Encoder {
public:
  Encoder(uint32_t pinA, uint32_t pinB);

  struct Update {
  public:
    inline bool active()        const { return _dir != 0; }
    inline int dir()            const { return _dir; }
      // -1 for CCW, 0 for no motion, and 1 for CW
    inline int accel(int rate)  const { return _dir + _dir * _speedup * rate; }

  private:
    Update(int16_t dir, int16_t speedup) : _dir(dir), _speedup(speedup) { }
    int16_t _dir;
    int16_t _speedup;

    friend class Encoder;
  };

  Update update();

private:
  const uint32_t pinA;
  const uint32_t pinB;

  int a;
  int b;

  int quads;

  unsigned long lastUpdate;
};



/* Buttons follow one of two cycles:

  Down -> Up
or
  Down -> DownLong -> UpLong

  There may be any number of NoChange states anywhere during these.
*/

class Button {
public:
    enum State {
      NoChange = 0,   // returned from update() if no change
      Down,
      DownLong,
      Up,
      UpLong
    };

    Button(uint32_t pin);
    State update();    // reports any action
    inline bool active()
      { return state == Down || state == DownLong; }

private:
    const uint32_t pin;

    int lastRead;
    unsigned long validAtTime;

    State state;
    unsigned long longAtTime;
};



class IdleTimeout {
public:
  IdleTimeout(unsigned long period);
  void activity();
  bool update();      // returns true on start of idle

private:
  const unsigned long period;
  bool idle;
  unsigned long idleAtTime;
};


#endif // _INCLUDE_UI_INPUT_H_
